Curse07-workprofile/LaserCut-Car/Model+Cut_Files/parts/front_grill_draft.SLDPRT

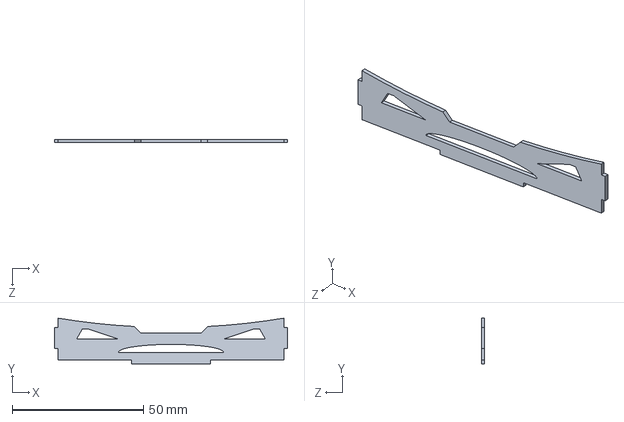
[picture p22: CAD file, 2025-09-22]
Model+Cut_Files/parts/front_grill_draft.SLDPRT
88.8 x 17.4 x 1.30 mm
