Curse07-workprofile/LaserCut-Car/Model+Cut_Files/parts/middle_part_draft.SLDPRT

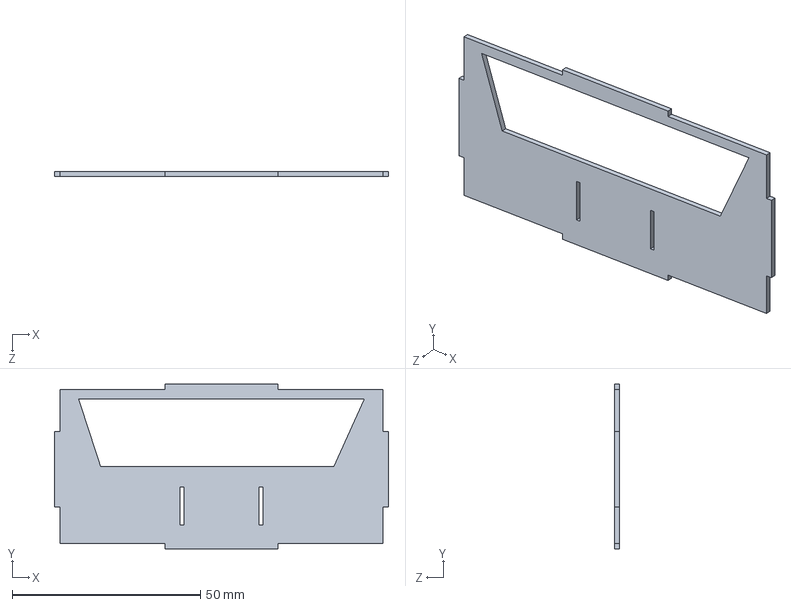
[picture p23: CAD file, 2025-09-22]
Model+Cut_Files/parts/middle_part_draft.SLDPRT
88.8 x 43.8 x 1.30 mm
