Curse07-workprofile/LaserCut-Car/Model+Cut_Files/parts/super_charger_draft.SLDPRT

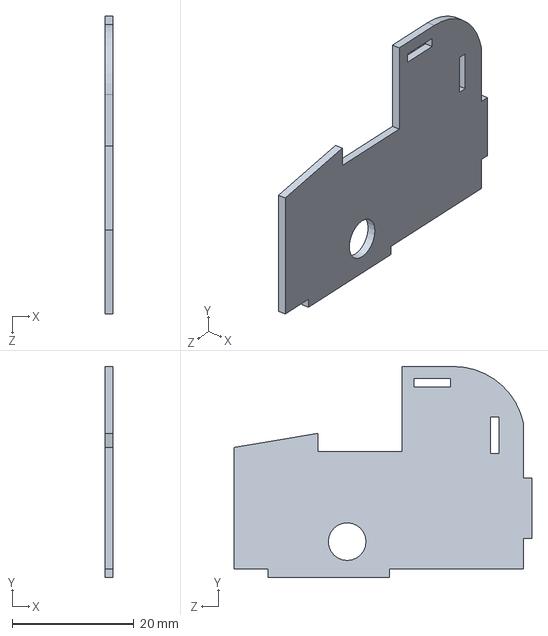
[picture p24: CAD file, 2025-09-22]
Model+Cut_Files/parts/super_charger_draft.SLDPRT
1.30 x 34.7 x 49.0 mm
