Curse07-workprofile/LaserCut-Car/Model+Cut_Files/parts/Engine_joint2_draft.SLDPRT

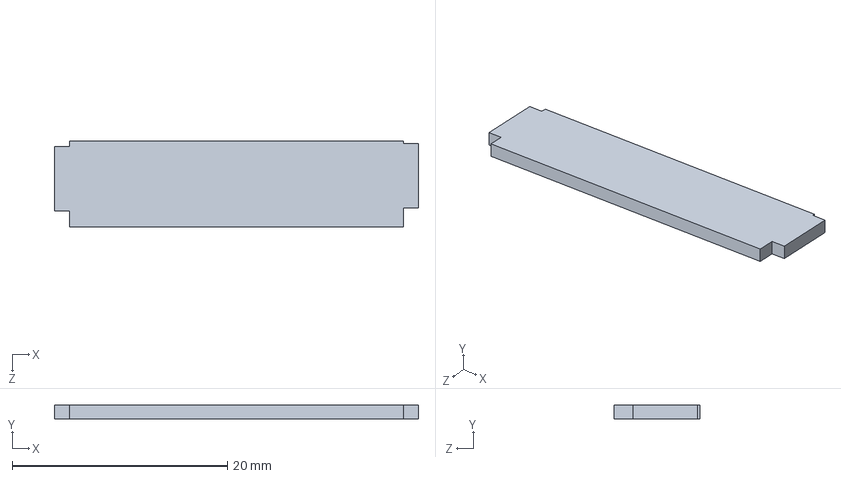
[picture p25: CAD file, 2025-09-22]
Model+Cut_Files/parts/Engine_joint2_draft.SLDPRT
33.8 x 1.30 x 8.00 mm
