Curse07-workprofile/LaserCut-Car/Model+Cut_Files/parts/base_plate_draft.SLDPRT

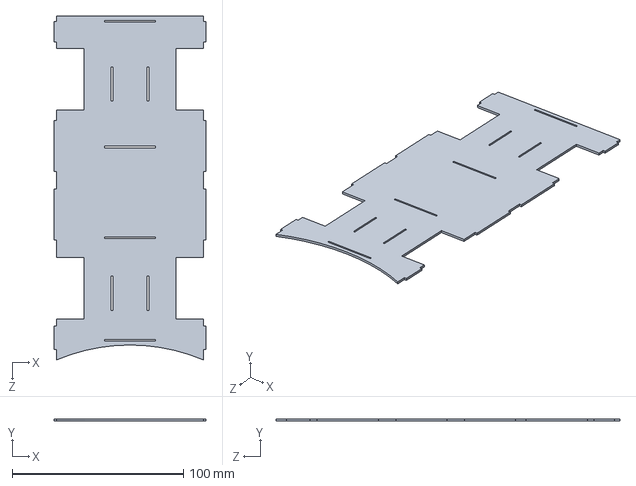
[picture p26: CAD file, 2025-09-22]
Model+Cut_Files/parts/base_plate_draft.SLDPRT
88.8 x 1.30 x 201.0 mm
