Curse07-workprofile/LaserCut-Car/Model+Cut_Files/parts/draft_axel.SLDPRT

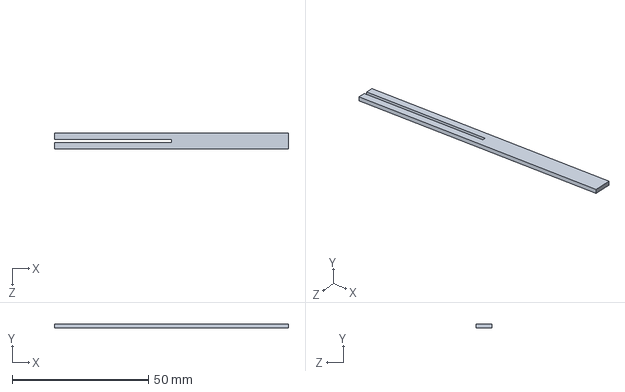
[picture p27: CAD file, 2025-09-22]
Model+Cut_Files/parts/draft_axel.SLDPRT
86.0 x 1.30 x 6.00 mm
