Curse07-workprofile/LaserCut-Car/Model+Cut_Files/parts/side_part_draft.SLDPRT

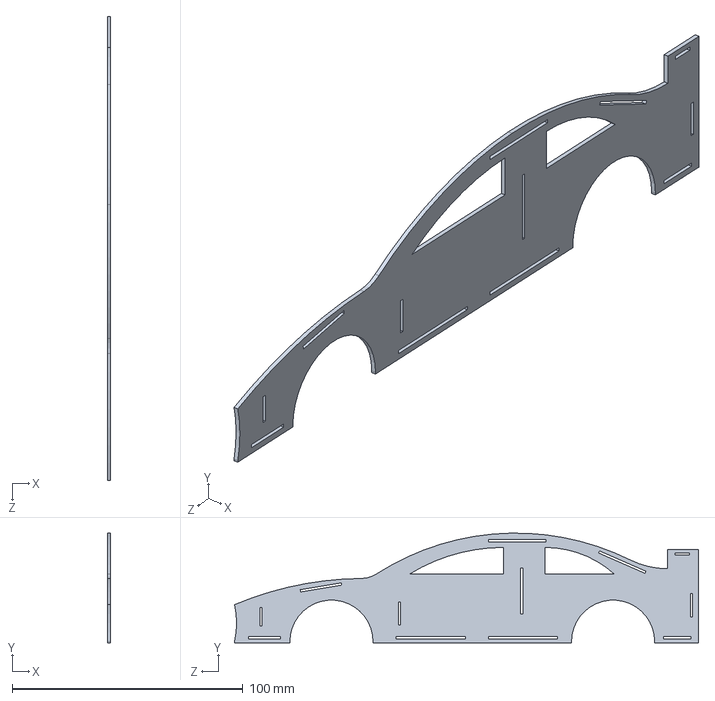
[picture p28: CAD file, 2025-09-22]
Model+Cut_Files/parts/side_part_draft.SLDPRT
1.30 x 47.5 x 201.0 mm
