Curse07-workprofile/LaserCut-Car/Model+Cut_Files/parts/back_plate_draft.SLDPRT

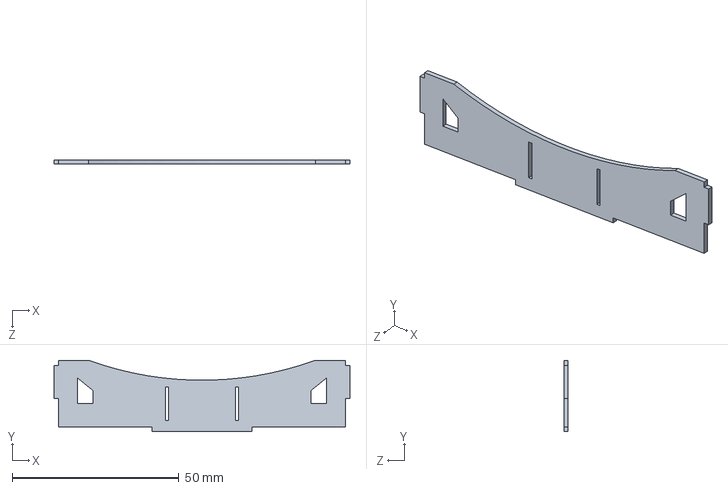
[picture p29: CAD file, 2025-09-22]
Model+Cut_Files/parts/back_plate_draft.SLDPRT
88.8 x 21.4 x 1.30 mm
