Curse07-workprofile/LaserCut-Car/Model+Cut_Files/parts/Engine_joint_draft.SLDPRT

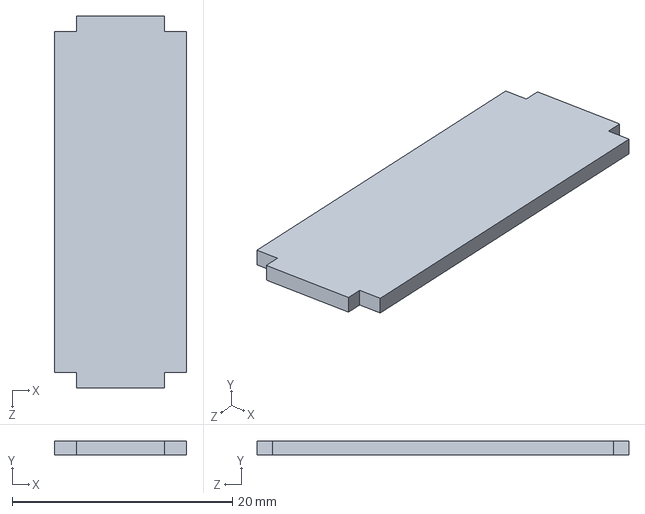
[picture p30: CAD file, 2025-09-22]
Model+Cut_Files/parts/Engine_joint_draft.SLDPRT
12.0 x 1.30 x 33.8 mm
